brolam/OpenHomeAnalysis/Android/appSupervisory/src/main/java/br/com/brolam/oha/supervisory/data/OhaEnergyUseProvider.java

package br.com.brolam.oha.supervisory.data;

import android.annotation.TargetApi;
import android.content.ContentProvider;
import android.content.ContentValues;
import android.content.UriMatcher;
import android.database.Cursor;
import android.database.SQLException;
import android.database.sqlite.SQLiteDatabase;
import android.net.Uri;
import android.provider.BaseColumns;
import android.support.annotation.NonNull;
import android.support.annotation.Nullable;
import android.util.Pair;

import java.util.Date;
import java.util.HashMap;
import java.util.HashSet;
import java.util.Set;
import java.util.TreeSet;

import br.com.brolam.library.helpers.OhaHelper;
import br.com.brolam.oha.supervisory.data.cursors.IOhaEnergyUseTotalCache;
import br.com.brolam.oha.supervisory.data.cursors.OhaEnergyUseBillCursor;
import br.com.brolam.oha.supervisory.data.cursors.OhaEnergyUseDaysCursor;
import br.com.brolam.oha.supervisory.data.helpers.OhaSQLHelper;

import static br.com.brolam.oha.supervisory.data.OhaEnergyUseContract.*;

/**
 * Disponibilizar informações da utilização de energia através de um ContentProvider
 * @author Breno Marques
 * @version 1.00
 * @since Release 01
 */
public class OhaEnergyUseProvider extends ContentProvider implements IOhaEnergyUseTotalCache {

    //Definir os códigos que serão relacionados as URIs para facilitar a identificaçãos das mesmas.
    public static final int CODE_ENERGY_USER_LOG = 100;
    public static final int CODE_ENERGY_USER_DAYS = 200;
    public static final int CODE_ENERGY_USER_BILL = 300;
    //Esse UriMatcher será utilizado para realicionar as URIs as códigos supracitados.
    private static final UriMatcher sUriMatcher = buildUriMatcher();
    private OhaSQLHelper ohaSQLHelper;
    //Hash para armazenar o cache com os totais de utilização de energia.
    private HashMap<Pair<Long,Long>,HashMap<Integer,String>> hashEnergyUseTotalCache;

    public static UriMatcher buildUriMatcher() {
        final UriMatcher matcher = new UriMatcher(UriMatcher.NO_MATCH);
        //Mapeamento das URIs referente aos logs de utilização de energia:
        final String energyUseLogAuthority = OhaEnergyUseContract.CONTENT_AUTHORITY;
        matcher.addURI(energyUseLogAuthority, PATH_LOG, CODE_ENERGY_USER_LOG);
        matcher.addURI(energyUseLogAuthority, PATH_DAYS, CODE_ENERGY_USER_DAYS);
        matcher.addURI(energyUseLogAuthority, PATH_BILL, CODE_ENERGY_USER_BILL);
        return matcher;
    }

    @Override
    public boolean onCreate() {
        this.ohaSQLHelper = new OhaSQLHelper(getContext());
        this.hashEnergyUseTotalCache = new HashMap<>();
        return true;
    }

    @Override
    public int bulkInsert(@NonNull Uri uri, @NonNull ContentValues[] values) {
        SQLiteDatabase sqLiteDatabase = this.ohaSQLHelper.getWritableDatabase();
        switch (sUriMatcher.match(uri)) {
            case CODE_ENERGY_USER_LOG:
                return bulkInsertEnergyUseLogs(uri, values, sqLiteDatabase);
            default:
                throw new UnsupportedOperationException("Unknown uri: " + uri);
        }
    }

    @Nullable
    @Override
    public Uri insert(@NonNull Uri uri, @Nullable ContentValues contentValues) {
        SQLiteDatabase sqLiteDatabase = this.ohaSQLHelper.getWritableDatabase();
        switch (sUriMatcher.match(uri)) {
            case CODE_ENERGY_USER_BILL:
                long id = insertEnergyUseBill(uri, contentValues, sqLiteDatabase);
                return CONTENT_URI_BILL.buildUpon().appendPath(String.valueOf(id)).build();
            default:
                throw new UnsupportedOperationException("Unknown uri: " + uri);
        }
    }

    @Nullable
    @Override
    public Cursor query(@NonNull Uri uri, @Nullable String[] projection, @Nullable String selection, @Nullable String[] selectionArgs, @Nullable String sortOrder) {
        SQLiteDatabase sqLiteDatabase = this.ohaSQLHelper.getReadableDatabase();
        switch (sUriMatcher.match(uri)) {
            case CODE_ENERGY_USER_LOG:
                return getOhaEnergyUseLogCursor(sqLiteDatabase, projection, selection, selectionArgs, sortOrder);
            case CODE_ENERGY_USER_DAYS:
                return getOhaEnergyUseDaysCursor(sqLiteDatabase, uri);
            case CODE_ENERGY_USER_BILL:
                String strID = uri.getQueryParameter(EnergyUseBillEntry._ID);
                if ( strID != null){
                    return sqLiteDatabase.query(EnergyUseBillEntry.TABLE_NAME, projection, String.format("%s = ?", EnergyUseBillEntry._ID), new String[]{strID}, null, null, null);
                }
                return getOhaEnergyUseBillCursor(sqLiteDatabase, selection, selectionArgs, sortOrder);
            default:
                throw new UnsupportedOperationException("Unknown uri: " + uri);
        }
    }

    @Nullable
    @Override
    public String getType(@NonNull Uri uri) {
        throw new UnsupportedOperationException("Unknown uri: " + uri);
    }

    @Override
    public int delete(@NonNull Uri uri, @Nullable String s, @Nullable String[] strings) {
        SQLiteDatabase sqLiteDatabase = this.ohaSQLHelper.getWritableDatabase();
        switch (sUriMatcher.match(uri)) {
            case CODE_ENERGY_USER_BILL:
                String strID = uri.getQueryParameter(EnergyUseBillEntry._ID);
                if ( strID != null){
                   int deleted = sqLiteDatabase.delete(EnergyUseBillEntry.TABLE_NAME, String.format("%s = ?", EnergyUseBillEntry._ID), new String[]{strID});
                    //Notificar a atualização para as Uri relacionadas a tabela EnergyUseBill
                    notifyUpdatedEntities(uri);
                    return deleted;
                }
            default:
                throw new UnsupportedOperationException("Unknown uri: " + uri);
        }
    }

    @Override
    public int update(@NonNull Uri uri, @Nullable ContentValues contentValues, @Nullable String s, @Nullable String[] strings) {
        SQLiteDatabase sqLiteDatabase = this.ohaSQLHelper.getWritableDatabase();
        switch (sUriMatcher.match(uri)) {
            case CODE_ENERGY_USER_BILL:
                String strID = uri.getQueryParameter(EnergyUseBillEntry._ID);
                if ( strID != null){
                    int updated = sqLiteDatabase.update(EnergyUseBillEntry.TABLE_NAME, contentValues, String.format("%s = ?", EnergyUseBillEntry._ID), new String[]{strID});
                    //Notificar a atualização para as Uri relacionadas a tabela EnergyUseBill
                    notifyUpdatedEntities(uri);
                    return updated;
                }
            default:
                throw new UnsupportedOperationException("Unknown uri: " + uri);
        }
    }

    /**
     * You do not need to call this method. This is a method specifically to assist the testing
     * framework in running smoothly. You can read more at:
     * http://developer.android.com/reference/android/content/ContentProvider.html#shutdown()
     */
    @Override
    @TargetApi(11)
    public void shutdown() {
        this.ohaSQLHelper.close();
        super.shutdown();
    }

    /**
     * Recuperar um cursor com os logs de utilização de energia.
     */
    private Cursor getOhaEnergyUseLogCursor(SQLiteDatabase sqLiteDatabase, String[] projection, @Nullable String selection, @Nullable String[] selectionArgs, @Nullable String sortOrder) {
        return sqLiteDatabase.query(
                EnergyUseLogEntry.TABLE_NAME,
                projection,
                selection,
                selectionArgs,
                null,
                null,
                sortOrder
        );
    }

    /**
     * Recuperar um cursor {@link OhaEnergyUseDaysCursor} com a utilização de energia por dia.
     */
    private Cursor getOhaEnergyUseDaysCursor(SQLiteDatabase sqLiteDatabase, Uri uri) {
        String strEndDate = uri.getQueryParameter(PATH_DAYS_PARAM_END_DATE);
        Date endDate = OhaHelper.getDateEnd(strEndDate == null ? new Date() : new Date(Long.parseLong(strEndDate)), false);
        Cursor cursor = sqLiteDatabase.query(
                EnergyUseLogEntry.TABLE_NAME,
                EnergyUseLogEntry.COLUMNS_CALC_PERIOD,
                String.format("%s <= ?", EnergyUseLogEntry._ID),
                new String[]{Long.toString(endDate.getTime())},
                null,
                null,
                null);
        int count = 1;
        if (cursor.moveToFirst()) {
            long periodBegin =  OhaHelper.getDateBegin(new Date(cursor.getLong(EnergyUseLogEntry.INDEX_COLUMNS_CALC_PERIOD_BEGIN))).getTime();
            long periodEnd = OhaHelper.getDateEnd(new Date(cursor.getLong(EnergyUseLogEntry.INDEX_COLUMNS_CALC_PERIOD_END)), false).getTime();
            count = (int) OhaHelper.getAmountDays(periodBegin, periodEnd);
        }
        return new OhaEnergyUseDaysCursor(sqLiteDatabase, endDate, count, this);
    }

    /**
     * Recuperar um Cursor {@link OhaEnergyUseBillCursor} com a conta de energia e utilização no período da conta.
     */
    private Cursor getOhaEnergyUseBillCursor(SQLiteDatabase sqLiteDatabase, String selection, String[] selectionArgs, String sortOrder) {
        Cursor cursor = sqLiteDatabase.query(EnergyUseBillEntry.TABLE_NAME, EnergyUseBillEntry.COLUMN_ALL, selection, selectionArgs, null, null, sortOrder);
        //*Atualizar o cache de totais de utilização de energia para até 5 contas:
        for(int index = 0; index < 5 && index < cursor.getCount(); index++ ){
            cursor.moveToPosition(index);
            getEnergyUseTotalOnCache(cursor.getLong(EnergyUseBillEntry.INDEX_COLUMN_FROM), cursor.getLong(EnergyUseBillEntry.INDEX_COLUMN_TO) );
        }
        return  new OhaEnergyUseBillCursor(sqLiteDatabase, cursor, this);
    }


    /**
     * Inclusão em bloco dos logs de utilização de energia.
     */
    private int bulkInsertEnergyUseLogs(@NonNull Uri uri, @NonNull ContentValues[] values, SQLiteDatabase sqLiteDatabase) {
        sqLiteDatabase.beginTransaction();
        //Armazenar as datas dos novos logs para atualizar o cache de  utilização de energia.
        Set<Long> setDateUpdated = new TreeSet<>();
        try {
            for (int row = 0; row < values.length; row++) {
                ContentValues value = values[row];
                long insertedResult = sqLiteDatabase.insertWithOnConflict(
                        EnergyUseLogEntry.TABLE_NAME,
                        null,
                        value,
                        SQLiteDatabase.CONFLICT_REPLACE);
                if (insertedResult == -1) {
                    throw new SQLException(String.format("The EnergyUseLog content on the row %s It is not valid.", row));
                }
                setDateUpdated.add(value.getAsLong(EnergyUseLogEntry._ID));
            }
            sqLiteDatabase.setTransactionSuccessful();
        } finally {
            sqLiteDatabase.endTransaction();
        }
        //Atualizar o cache de  utilização de energia.
        updateEnergyUseTotalOnCache(setDateUpdated);
        //Notificar a atualização para as Uri relacionadas a tabela EnergyUseLog
        notifyUpdatedEntities(uri);
        return values.length;
    }

    /**
     * Inclusão de uma conta de energia.
     */
    private long insertEnergyUseBill(@NonNull Uri uri, @NonNull ContentValues values, SQLiteDatabase sqLiteDatabase) {
        long id = -1;
        sqLiteDatabase.beginTransaction();
        try {
            id = sqLiteDatabase.insert(
                    EnergyUseBillEntry.TABLE_NAME,
                    null,
                    values);
            sqLiteDatabase.setTransactionSuccessful();
        } finally {
            sqLiteDatabase.endTransaction();
        }
        //Notificar a atualização para as Uri relacionadas a tabela EnergyUseBill
        notifyUpdatedEntities(uri);
        return id;
    }

    /**
       Recuperar o total de utilização de energia do cache ou atualizar o cache ser for necessário.
     */
    @Override
    public HashMap<Integer,String> getEnergyUseTotalOnCache(long beginDate, long endDate) {
        Pair<Long, Long> pairKey = new Pair(beginDate, endDate);
        HashMap<Integer,String> mapCache = hashEnergyUseTotalCache.get(pairKey);;
        if ( (mapCache != null) ){
            return mapCache;
        } else {
            SQLiteDatabase sqLiteDatabase = this.ohaSQLHelper.getReadableDatabase();
            String selection = String.format("%s BETWEEN ? AND ?", EnergyUseLogEntry._ID);
            String selectionArgs[] = new String[]{Long.toString(beginDate), Long.toString(endDate)};
            Cursor cursor = sqLiteDatabase.query(
                    EnergyUseLogEntry.TABLE_NAME,
                    EnergyUseLogEntry.COLUMNS_CALC_TOTAL,
                    selection,
                    selectionArgs,
                    null,
                    null,
                    null
            );
            try {
                //Gerar o cache se existir utilização de energia no período informado.
                if ((cursor.moveToFirst()) && (cursor.getDouble(EnergyUseLogEntry.INDEX_COLUMN_CALC_DURATION_SUN) > 0)) {
                    mapCache = new HashMap<>();
                    for (int index = 0; index < cursor.getColumnCount(); index++) {
                        mapCache.put(index, cursor.getString(index));
                    }
                    this.hashEnergyUseTotalCache.put(pairKey, mapCache);
                }
            } finally {
                cursor.close();
            }
            return mapCache;
        }
    }

    /**
      Atualizar o cache de totais de utilização de energia.
     */
    private void updateEnergyUseTotalOnCache(Set<Long> setDateUpdated) {
        //Verificar quais itens do cache devem ser atualizados:
        HashSet<Pair<Long, Long>> isNeedUpdate = new HashSet<>();
        for (Long endDate : setDateUpdated) {
            for (Pair<Long, Long> key : hashEnergyUseTotalCache.keySet()) {
                if ((endDate >= key.first) && (endDate <= key.second)) {
                    isNeedUpdate.add(key);
                }
            }
        }
        //Atualizar os itens do cache que precisam ser atualizados:
        for (Pair<Long, Long> key : isNeedUpdate) {
            hashEnergyUseTotalCache.remove(key);
            getEnergyUseTotalOnCache(key.first, key.second);
        }
    }

    /*
    Notificar a atualização para as Uris relacionadas a todas as tabelas desse provider
     */
    private void notifyUpdatedEntities(Uri uri) {
        getContext().getContentResolver().notifyChange(uri, null);
        if (!uri.equals(OhaEnergyUseContract.CONTENT_URI_DAYS))
            getContext().getContentResolver().notifyChange(OhaEnergyUseContract.CONTENT_URI_DAYS, null);
        if (!uri.equals(OhaEnergyUseContract.CONTENT_URI_BILL))
            getContext().getContentResolver().notifyChange(OhaEnergyUseContract.CONTENT_URI_BILL, null);
    }


}
